yuz207/agentpad13/release/hardware/case/v2/bases/INTERFACE.md

# agentpad13 — tray base interface

**Design your own base.** The tray carries four pockets near its centre. Put
four matching pegs on anything you like and it mounts. The interface does not
care how big your base is or what shape it is.

License: CERN-OHL-W v2. GENERATED by `agentpad13_base.py` — do not hand-edit.

## The datum

The centre of the case outline, in plan. The band outer
(95.6 x 111.4 mm) and the tray outline
(84.3 x 100.1 mm) are **both** centred on it, so you can find
it with a ruler on a finished case. Everything below is measured from there.

**Orientation.** The USB port is on the FAR edge, away from you. The pattern is
4-fold symmetric, so a base fits in any of four 90 deg rotations.

## The four pockets

| | |
|---|---|
| count | 4 |
| diameter | **Ø6.0 mm** |
| depth | **1.6 mm** below the mating plane |
| positions from datum | (-12.5, -12.5), (+12.5, -12.5), (-12.5, +12.5), (+12.5, +12.5) mm |
| square pitch | 25.0 mm (bolt circle Ø35.355) |
| mouth chamfer | 0.2 x 45 deg |
| mating plane | the flat tray bottom — keep all your material below it |

Smallest base that carries the whole pattern with a 3 mm wall:
**Ø47.4 mm.**

## Your pegs

| | |
|---|---|
| length | 1.4 mm — leaves a 0.2 mm gap so the base seats on its FACE, not on peg tips |
| tip chamfer | 0.4 mm |
| fit ladder | **5.6 / 5.7 / 5.8 / 5.9 mm** |
| start with | 5.8 in rigid filament, **5.9 in TPU** |

The tray side is CAD-nominal and carries **no** allowance — all the fit lives on
your peg. Print `stl/base_fit_gauge.stl`, push each peg into any pocket, keep
the rung that holds. The gauge is marked with raised dots: n dots = rung n,
smallest first.

TPU compresses instead of shearing the pocket wall, so it wants the **tight**
rung, not the loose one.

## Load path — read this before you make it thin

Vertical load goes through the **flat mating plane**, never through the pegs.
The pegs locate the base and take shear. Each has
8.4 mm2 of bearing, about 250 N at 30 MPa,
against single-digit-newton service loads. Engagement depth is not your limiting
factor; flatness of the mating face is.

## Keep-outs

- **BOOT / RESET service slots**, x 59.0..76.0, y 83.3..93.3 mm. If
  your base covers this area it **must** carry a through window. A base that
  stays inside **Ø78.36 mm**
  about the datum never reaches it.
- **Feet are not part of the design.** Every base underside is FLAT — no
  recesses, no bolt circle, no prescribed part. Stick on whatever you like,
  wherever you like; every stance figure below EXCLUDES feet.
- **USB face** is on the far edge, above the mating plane. A wedge that raises
  the far edge eats plug-to-desk clearance.

## Will it tip over? (small bases only)

The assembled pad is **176 g**, with its centre of mass within 1 mm of
the datum. A base narrower than the footprint makes it cantilever. The worst
load is a firm press on the **encoder knob edge**, 56 mm out — not the
farthest key.

Minimum base mass for a **circular** base, to hold a 1.5x margin at a 3 N press
and not tip at all at 5 N:

| diameter | >=1.5x at 3 N | no tip at 5 N |
|---|---|---|
| Ø50 | 401 g | 464 g |
| Ø60 | 228 g | 273 g |
| Ø65 | 162 g | 199 g |
| Ø70 | 105 g | 136 g |
| Ø74 | 65 g | 92 g |
| Ø78.0 | 29 g | 52 g |
| Ø80 | 13 g | 33 g |

**This is why the pedestal must be printed SOLID.** At Ø78 its own
printed mass is the only thing resisting the tip, so infill is a structural
setting here, not a speed one. A solid print clears the 5 N abuse case; a normal
3-wall / 20 % gyroid print clears the 3 N design case but not abuse. The
full-footprint `riser` and `wedge` need nothing at all — every control already
sits inside their support polygon.

Full method and the per-part mass model are in
`params/agentpad13_base_params.json` under `stability`. Several inputs are
estimates and are labelled as such — notably the encoder push force, which is
what sizes everything here.

## Reference bases in this folder

| variant | outline | mass | ballast |
|---|---|---|---|
| `riser` | 91.6 x 107.4 full footprint x 3 mm flat | 33 g | none |
| `wedge` | 91.6 x 107.4 full footprint, 8 deg back-raised | 50 g | none |
| `pedestal` | Ø78 tilted drum, 8 deg | 59 g | **print SOLID** — its own mass is the ballast |

All three print **desk face on the bed, no support**.
