yuz207/agentpad13/firmware/CODEX-OAI-SOURCE.md

# AgentPad13 direct-OAI source snapshot

This directory is the buildable source hand-off for the AgentPad13 Direct OAI
firmware. The original snapshot came from the `agentpad13-direct-oai` worktree
on branch `dev`, based at commit
`567efcba52709e7850540b5100361c0d85734b8e`, including the working-tree fixes
present when that snapshot was assembled. The destination port has since been
rebuilt from the reviewed AgentPad13 source; the current artifact facts below
supersede the snapshot candidate.
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
