yuz207/agentpad13/release/hardware/case/v2/bases/renders/bases.png

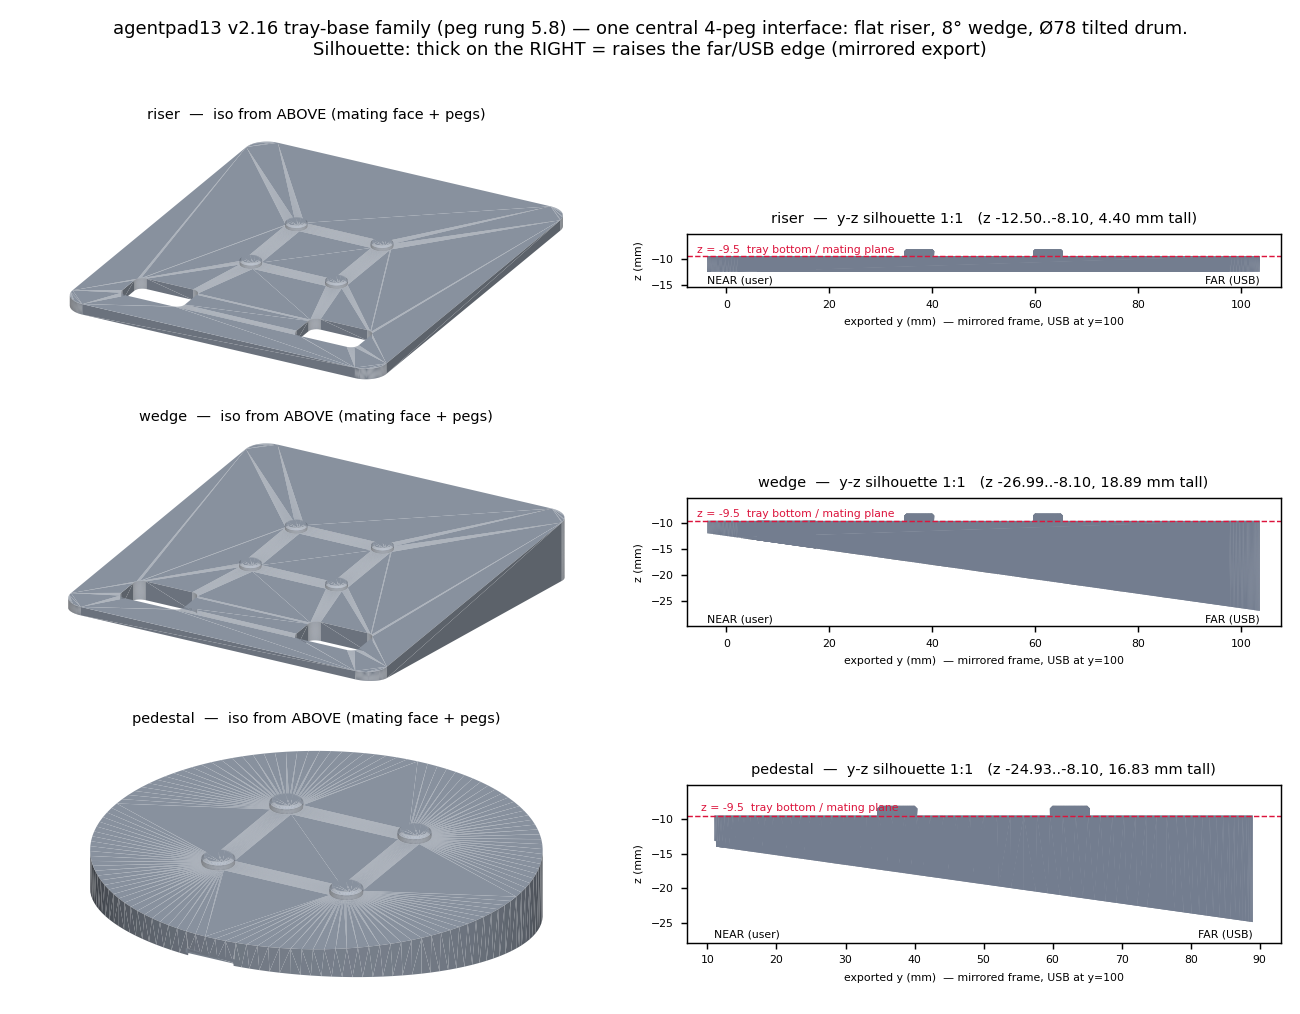
release/hardware/case/v2/bases/renders/bases.png
