yuz207/agentpad13/release/hardware/case/v2/fab/agentpad13_v2_plate_v5_top.png

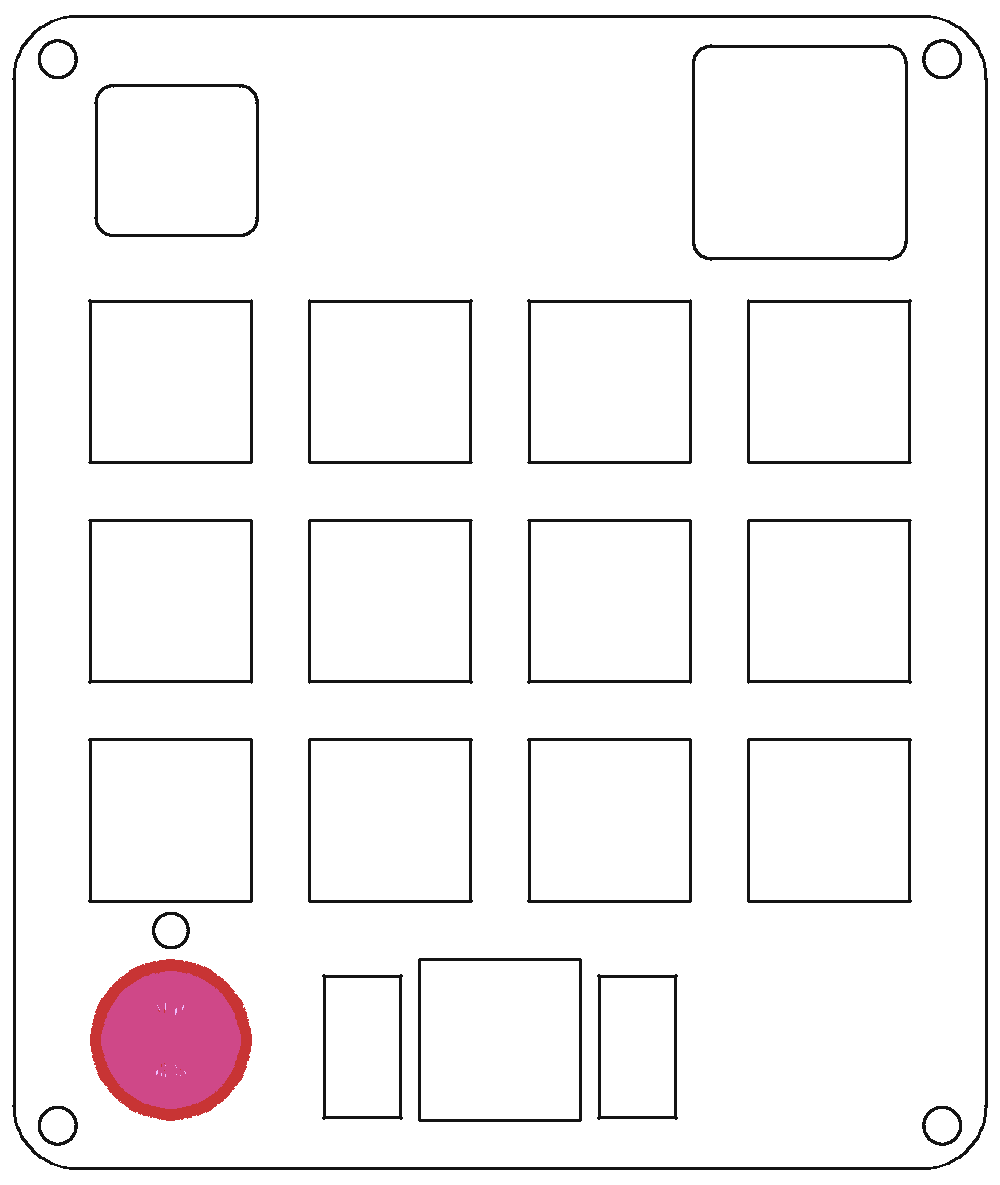
release/hardware/case/v2/fab/agentpad13_v2_plate_v5_top.png
