yuz207/agentpad13/release/hardware/case/v2/gasket/gasket_template.png

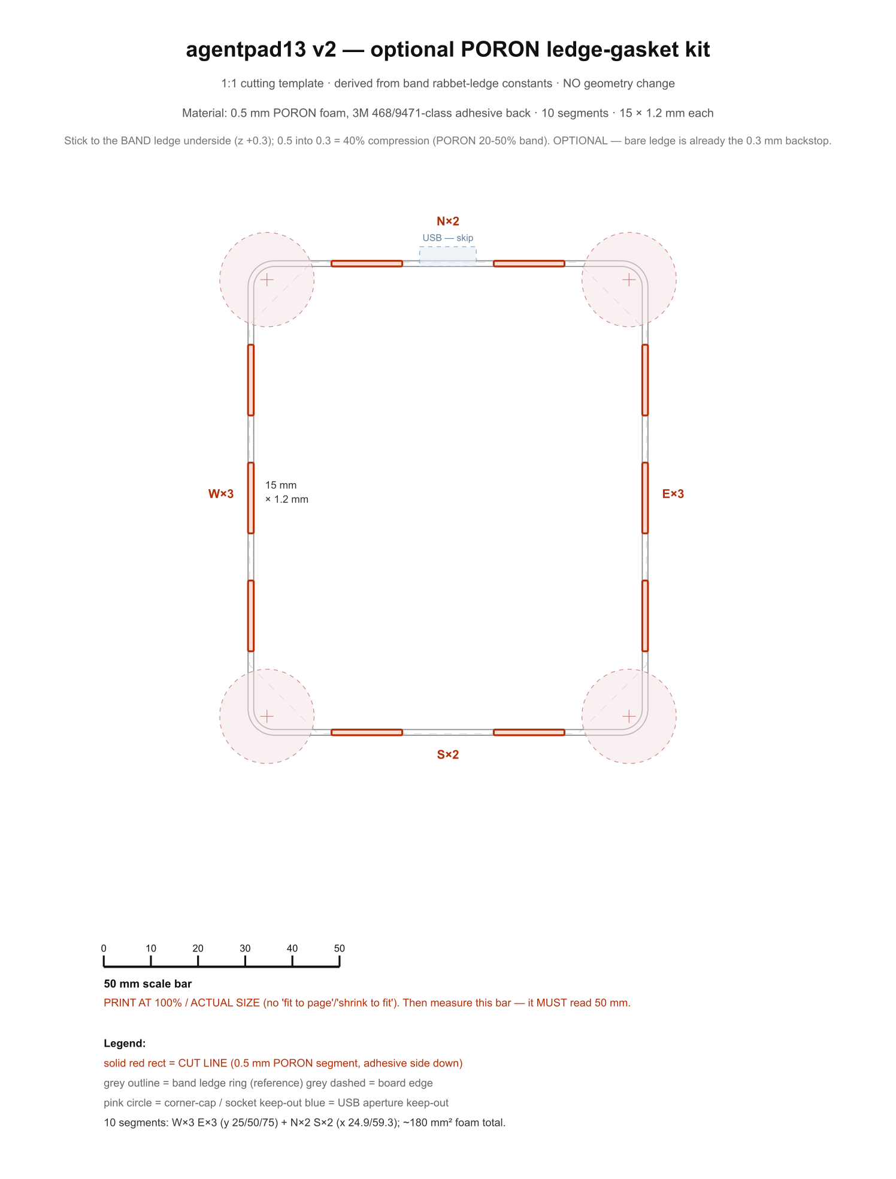
release/hardware/case/v2/gasket/gasket_template.png
