yuz207/agentpad13/release/hardware/pcb/v5_8_orient.png

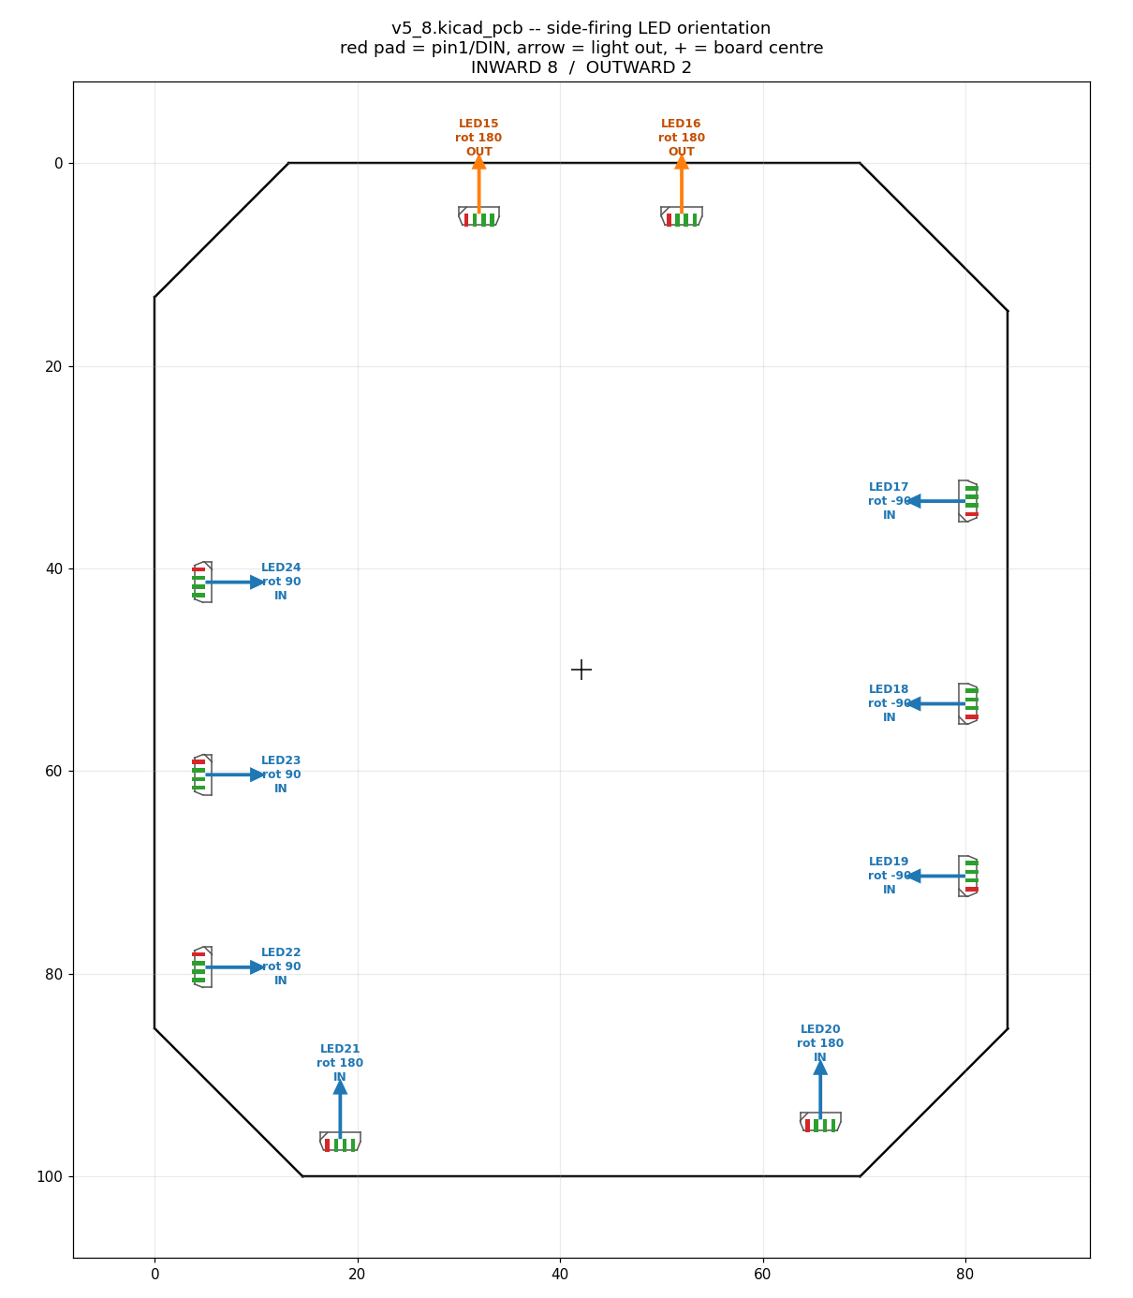
release/hardware/pcb/v5_8_orient.png
