yuz207/agentpad13/release/hardware/pcb/v5_8_render_top.png

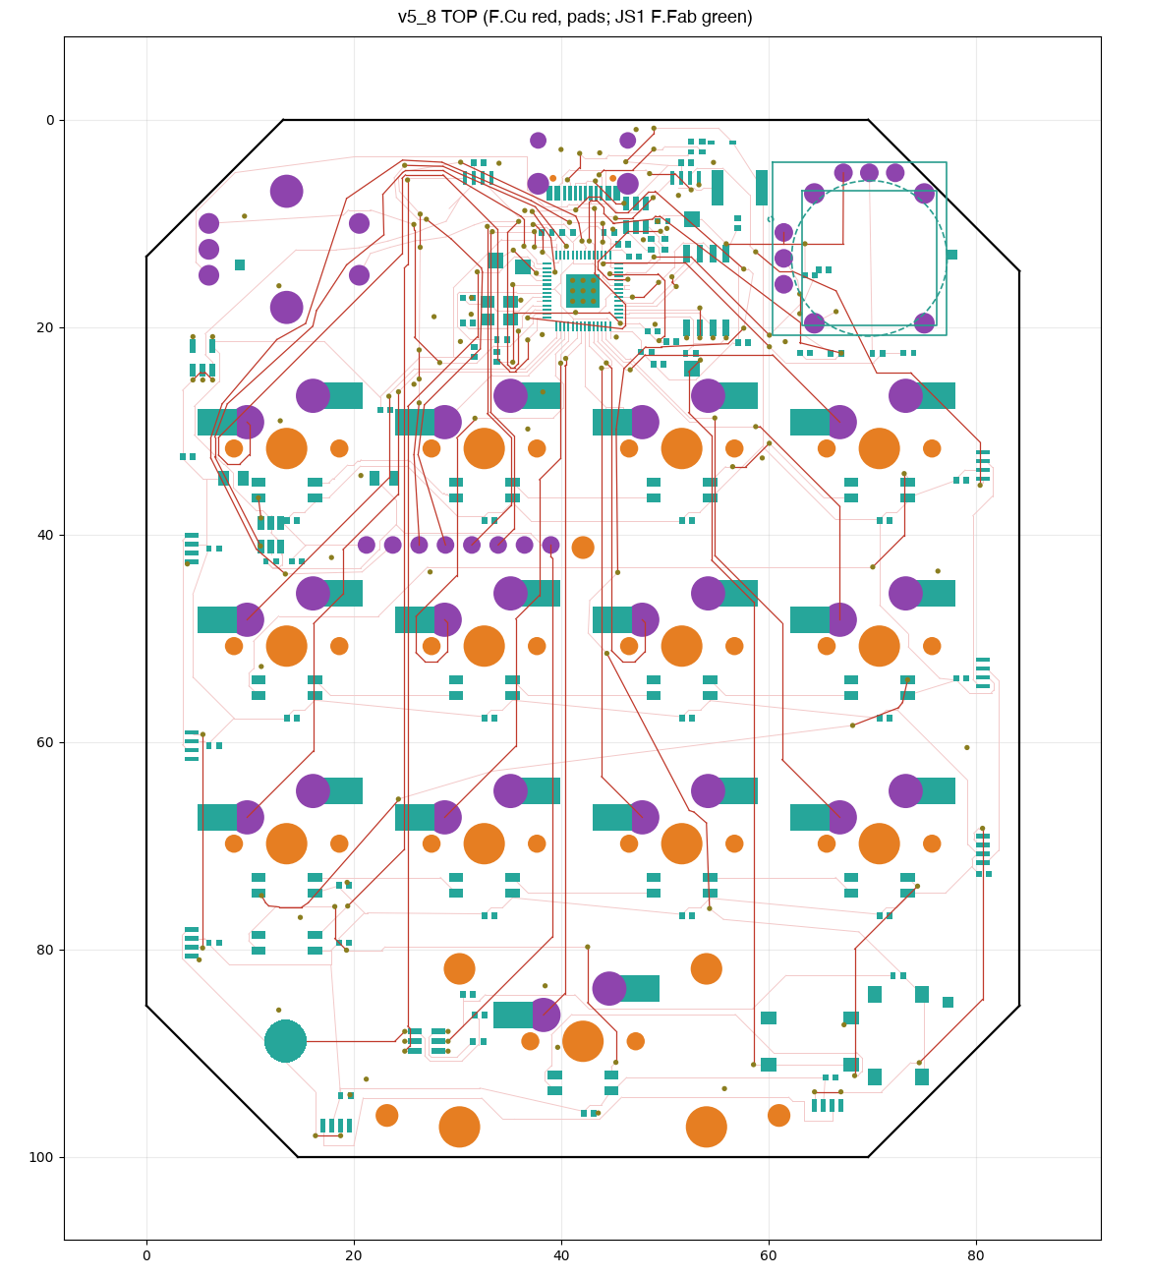
release/hardware/pcb/v5_8_render_top.png
