yuz207/agentpad13/release/renders/js1_pad_swap.png

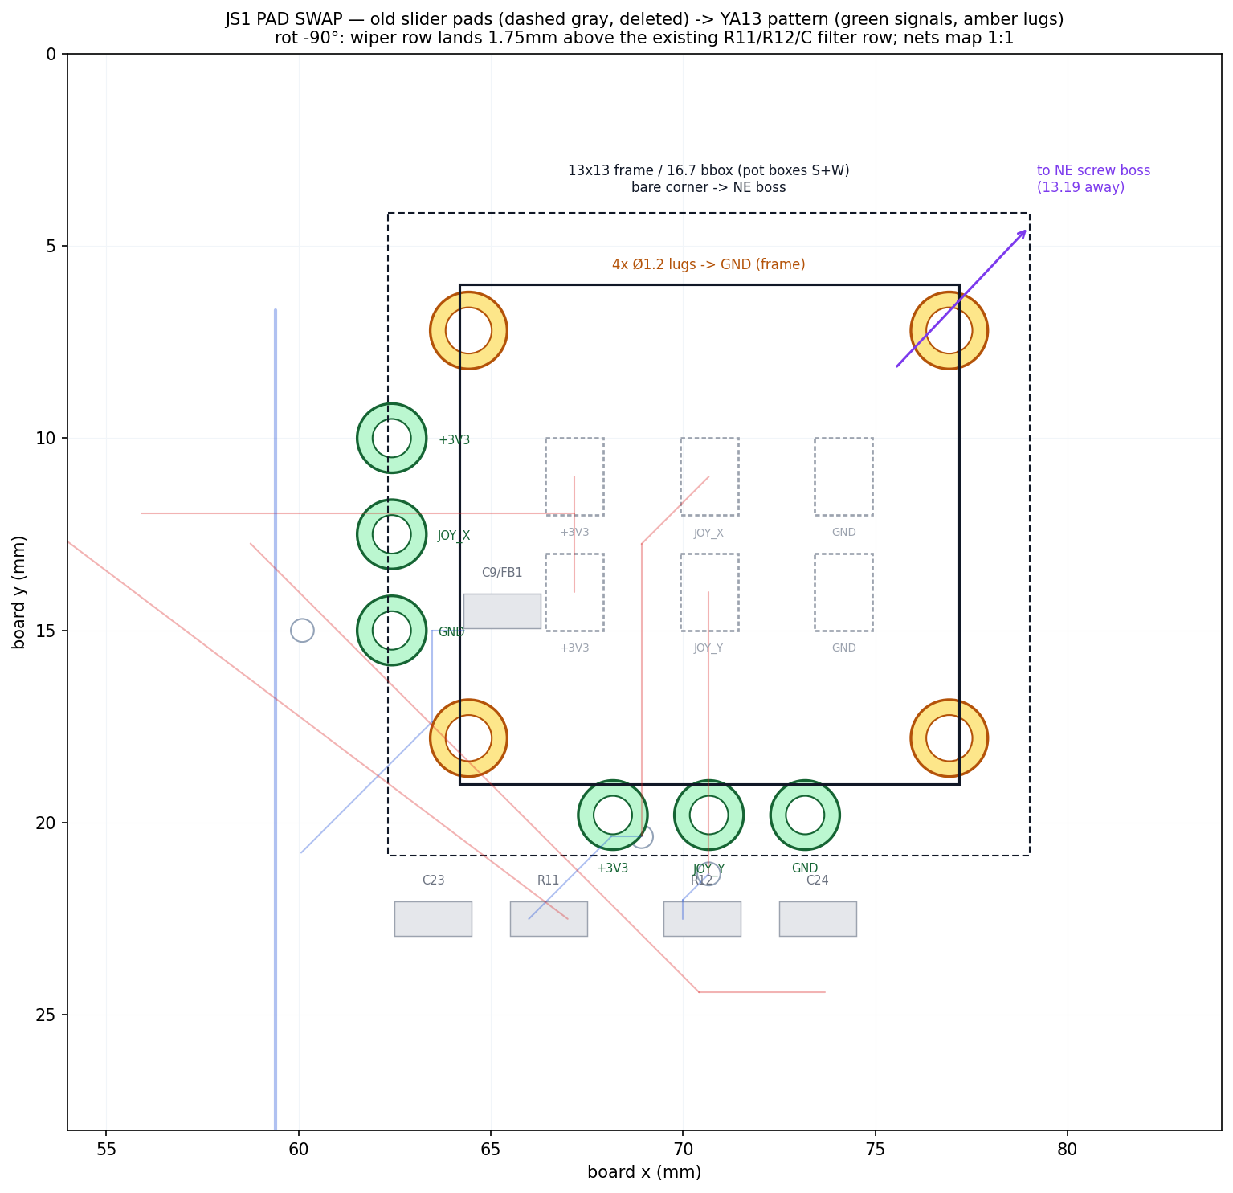
release/renders/js1_pad_swap.png
