yuz207/agentpad13/release/renders/v24_corner_notch.png

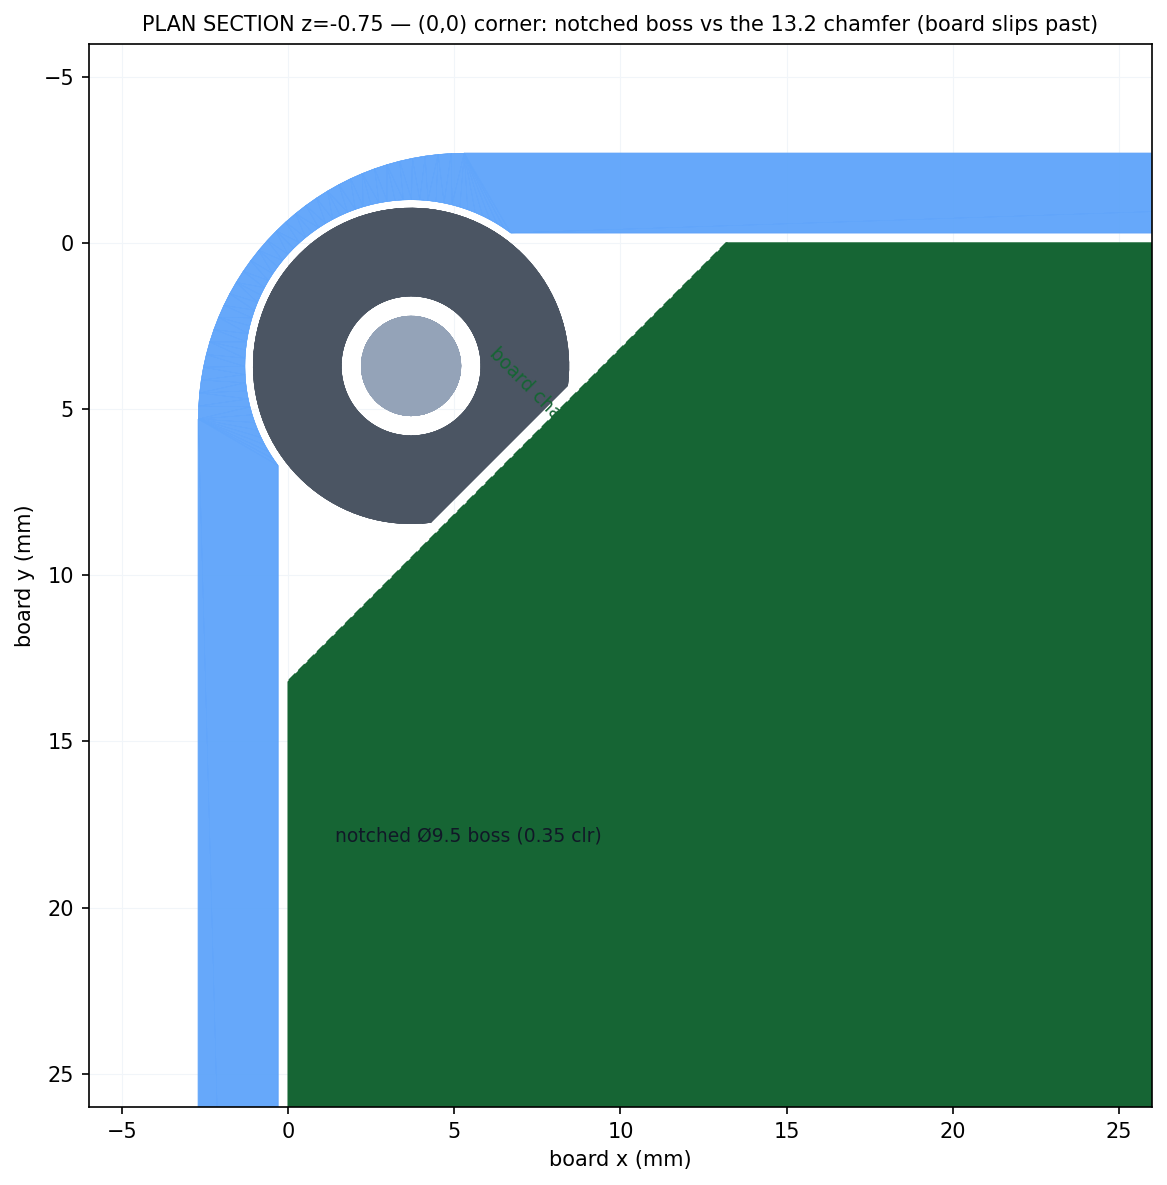
release/renders/v24_corner_notch.png
