yuz207/agentpad13/release/renders/v24_js_zone.png

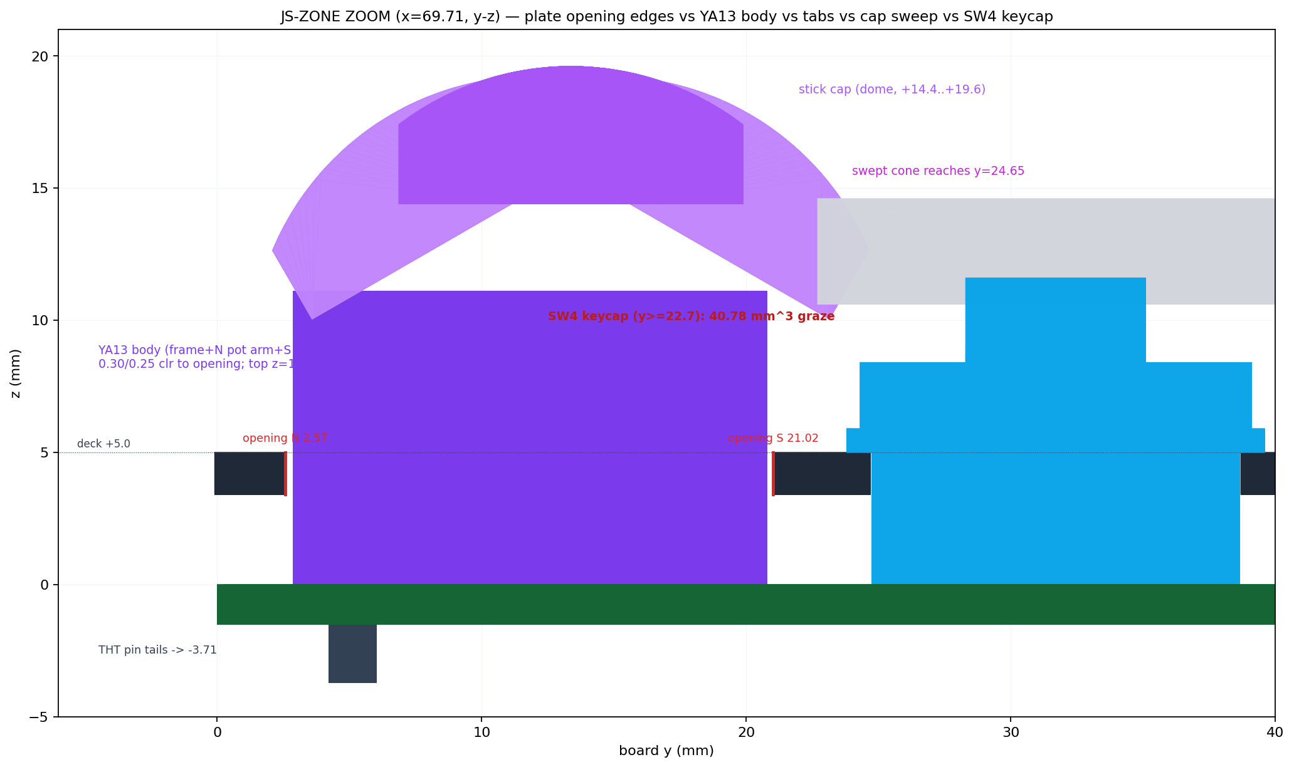
release/renders/v24_js_zone.png
