yuz207/agentpad13/release/renders/v24_js_zone_chamfer_STOP.png

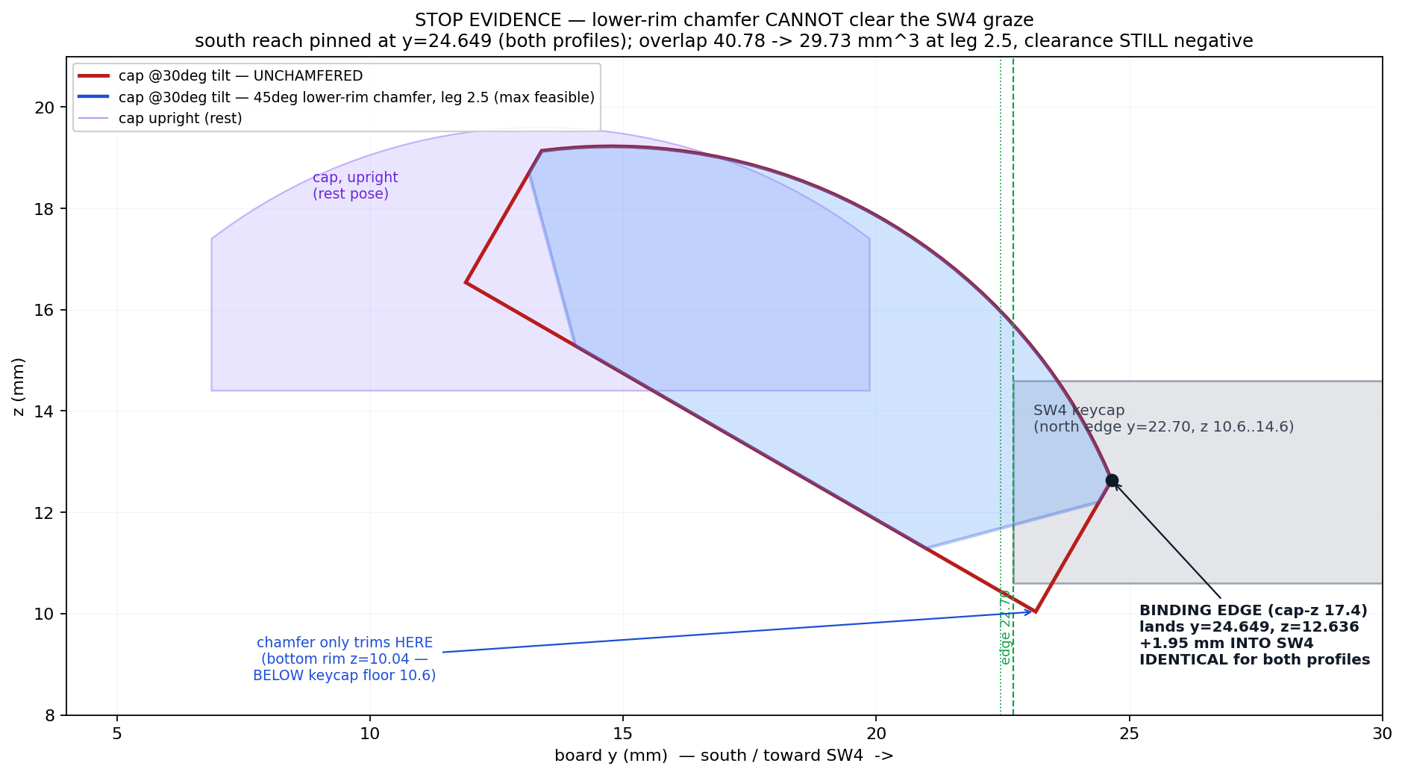
release/renders/v24_js_zone_chamfer_STOP.png
