yuz207/agentpad13/release/renders/v24_section_controls.png

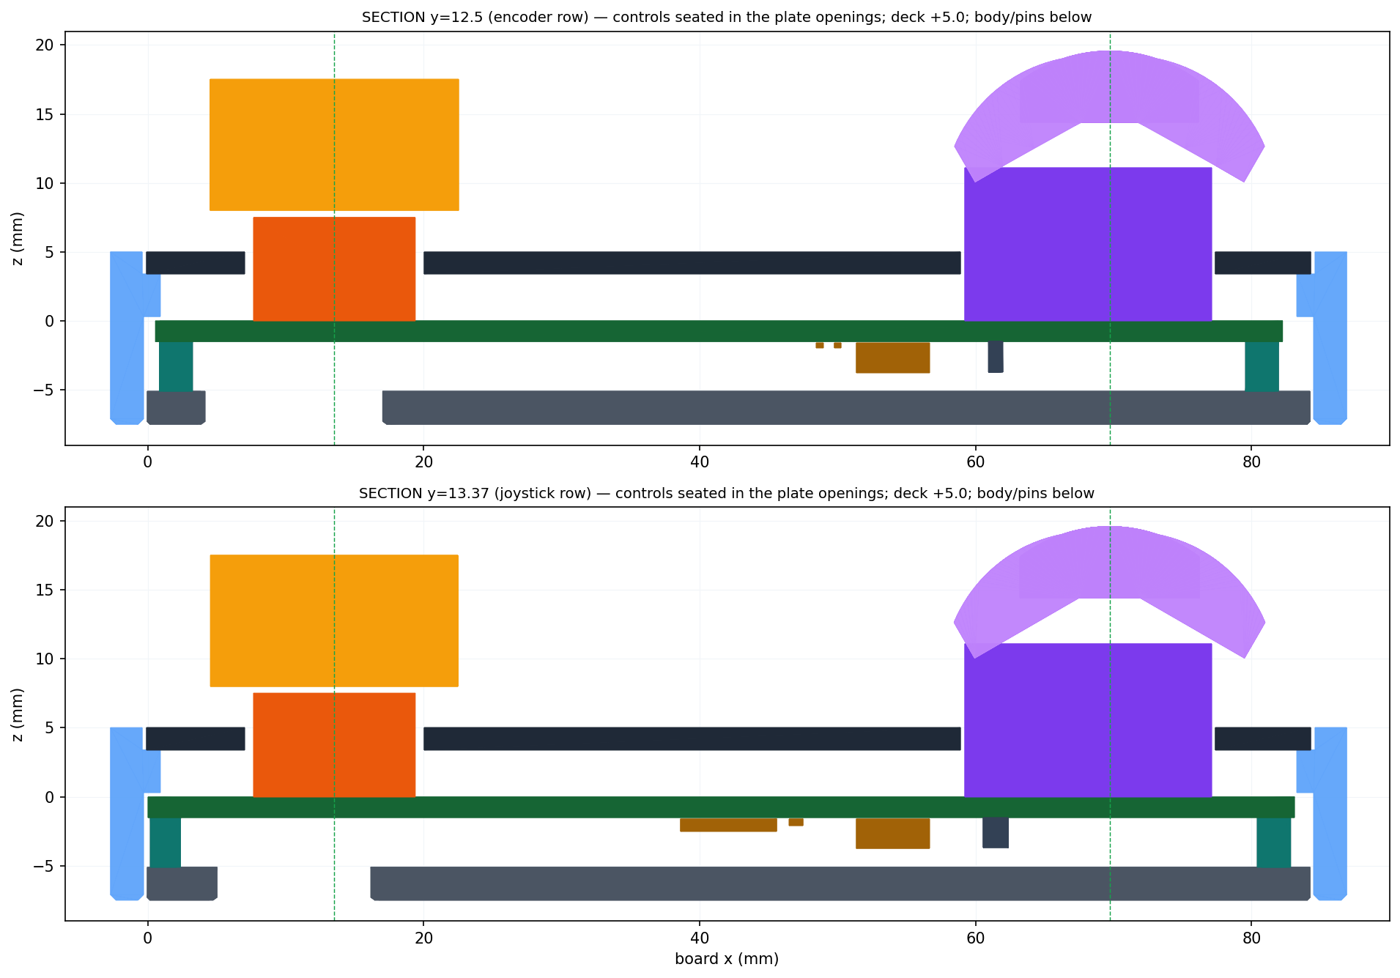
release/renders/v24_section_controls.png
