yuz207/agentpad13/release/renders/v24_section_stickcol.png

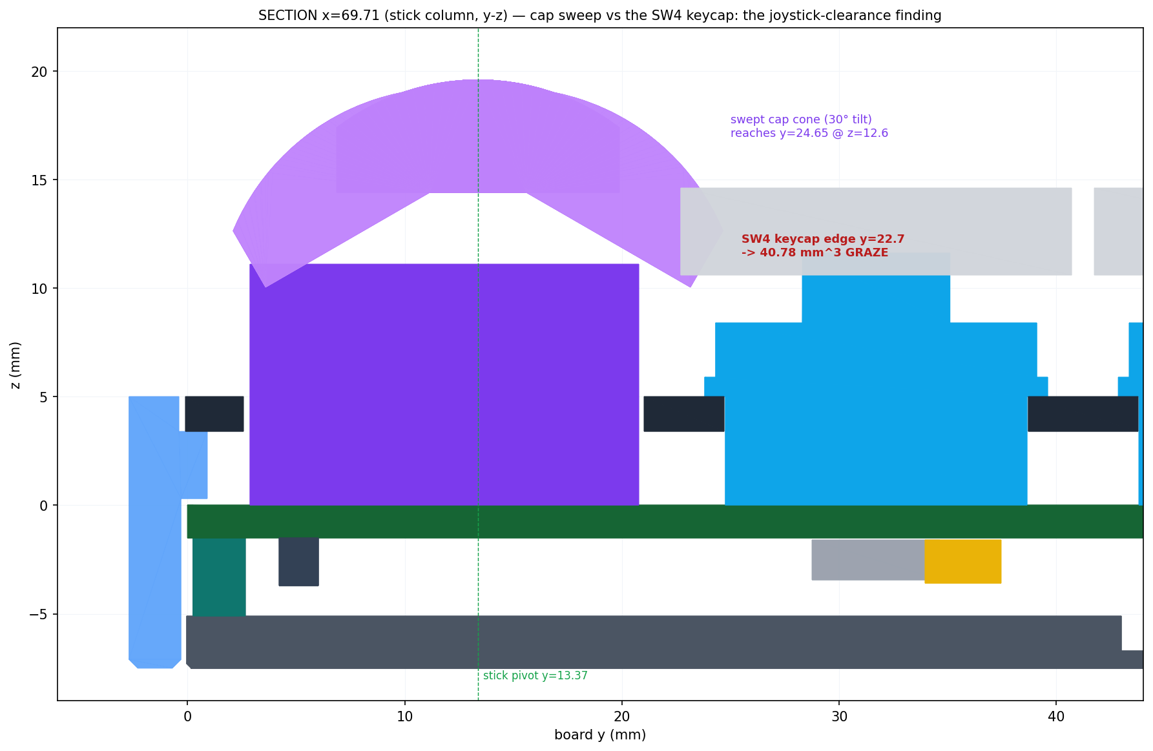
release/renders/v24_section_stickcol.png
