yuz207/agentpad13/release/renders/v24_section_usb.png

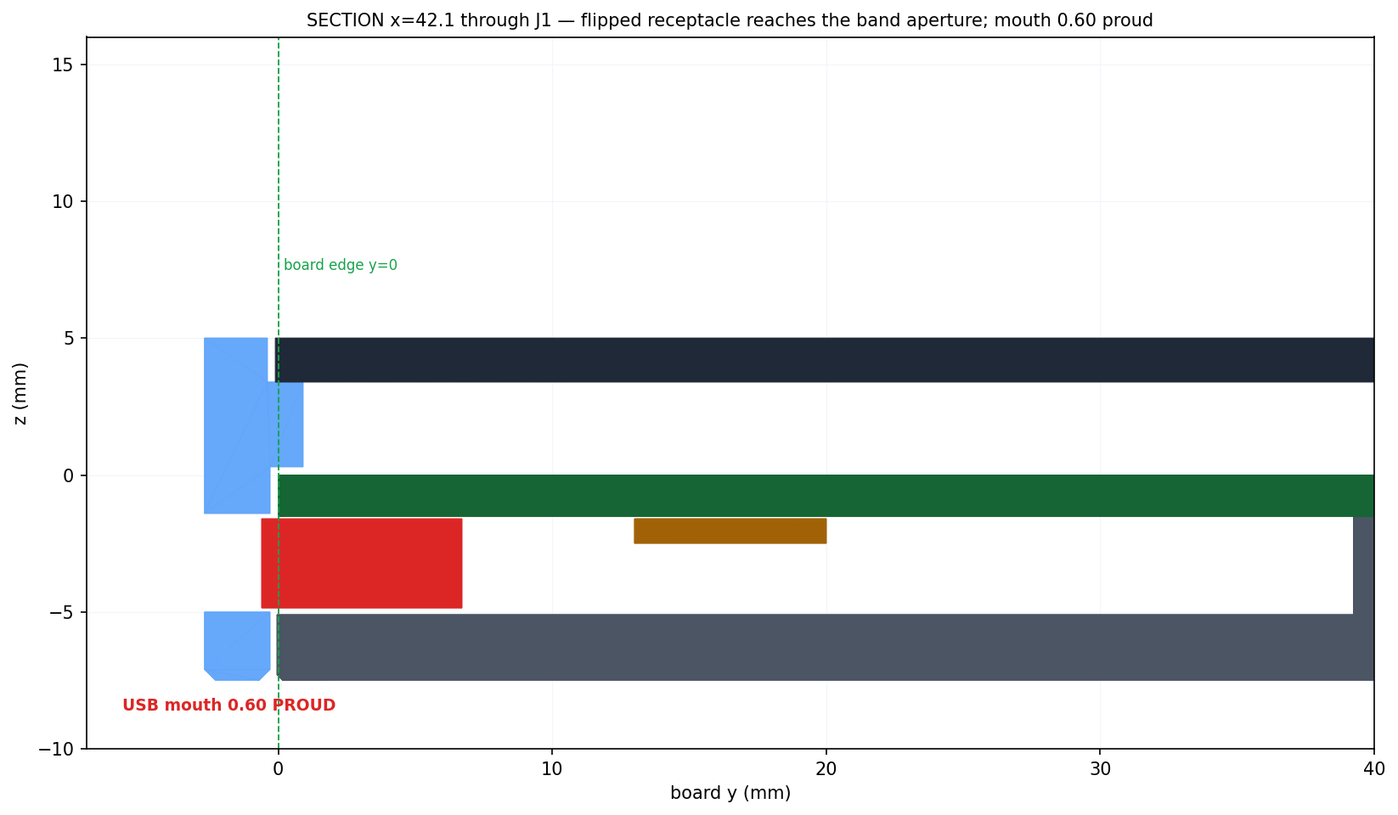
release/renders/v24_section_usb.png
