yuz207/agentpad13/release/renders/v24_side_elevations.png

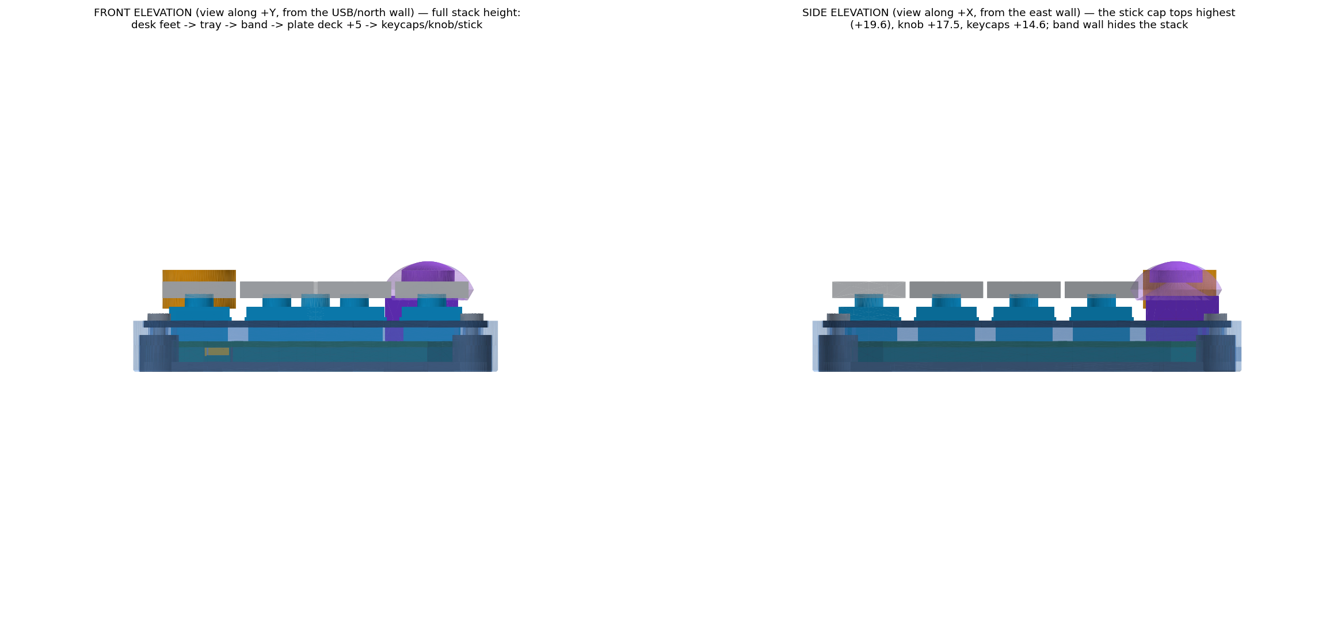
release/renders/v24_side_elevations.png
