yuz207/agentpad13/release/renders/v25_cap_taper_vs_dome.png

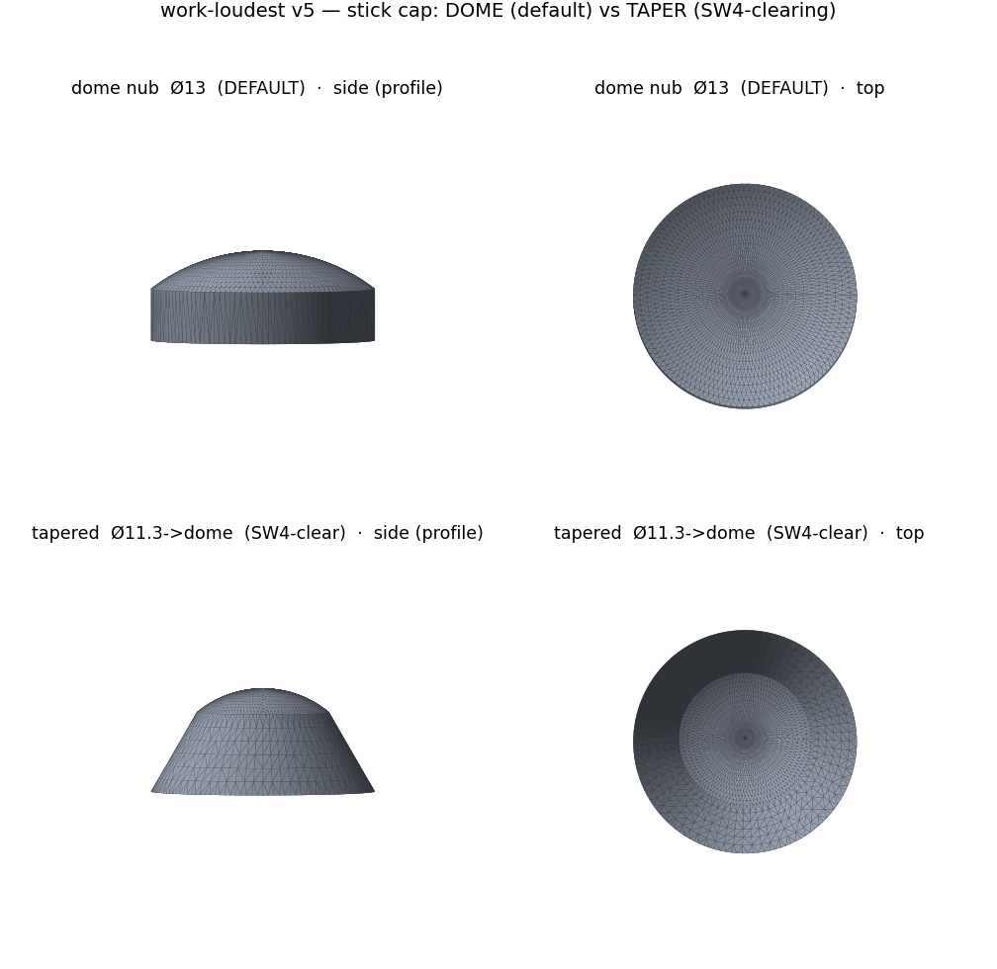
release/renders/v25_cap_taper_vs_dome.png
