yuz207/agentpad13/release/renders/v25_height_ladder.png

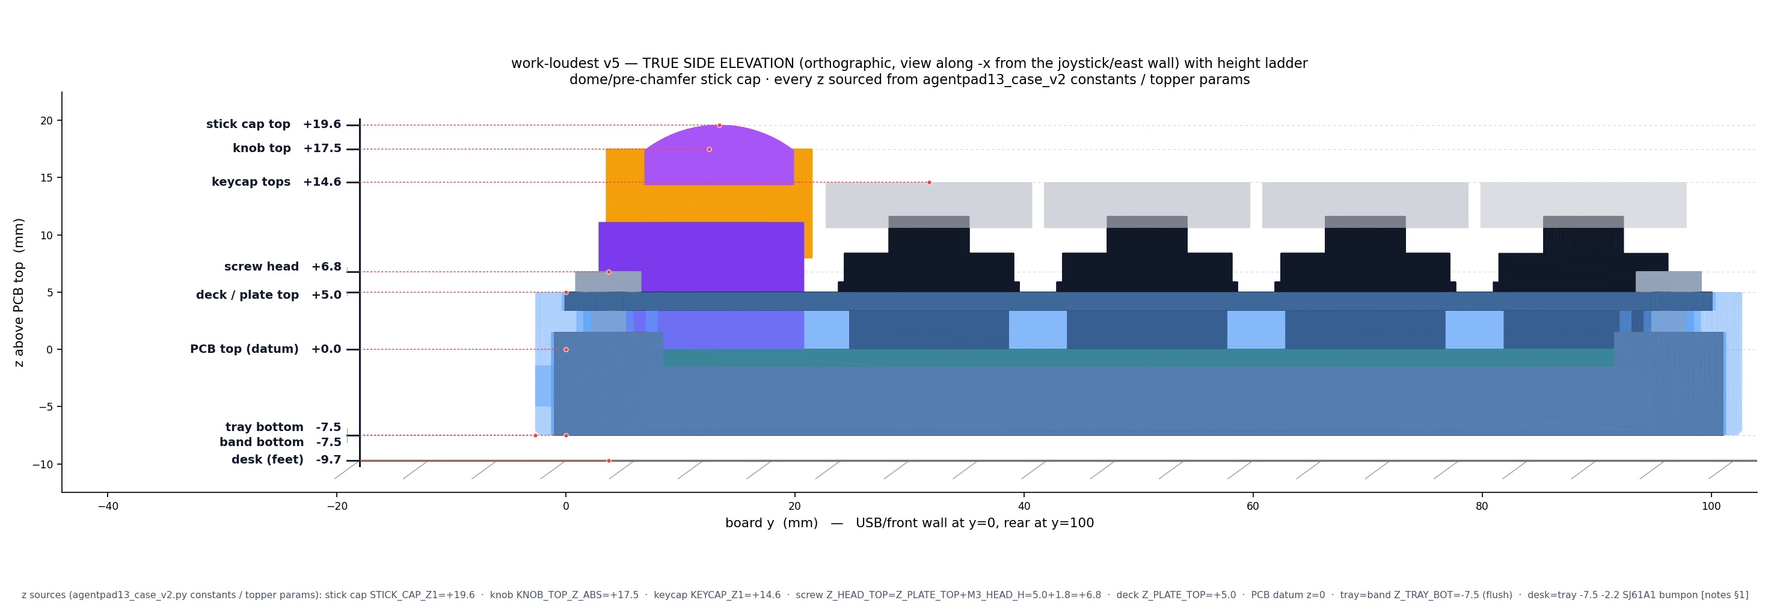
release/renders/v25_height_ladder.png
