yuz207/agentpad13/release/renders/v27_turntable.png

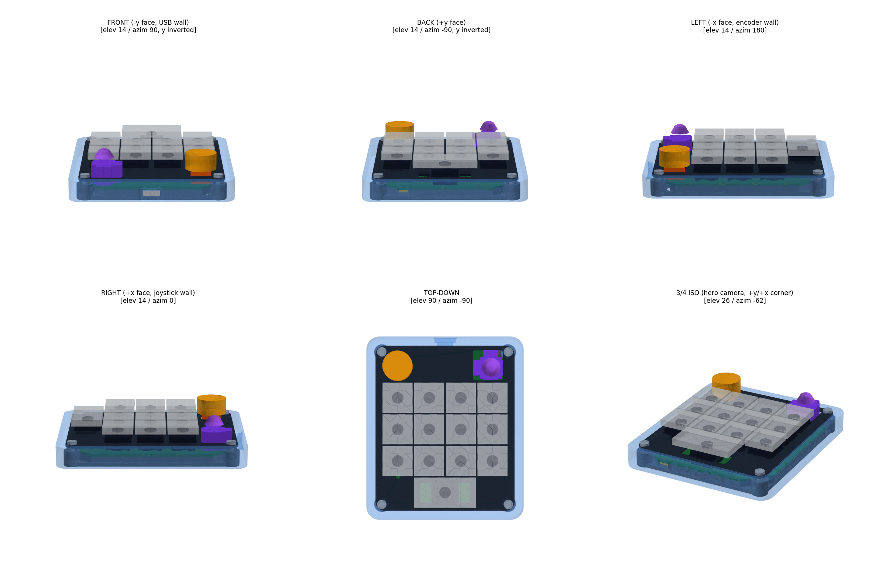
release/renders/v27_turntable.png
