yuz207/agentpad13/release/hardware/case/v2/step/agentpad13_v2_plate.step

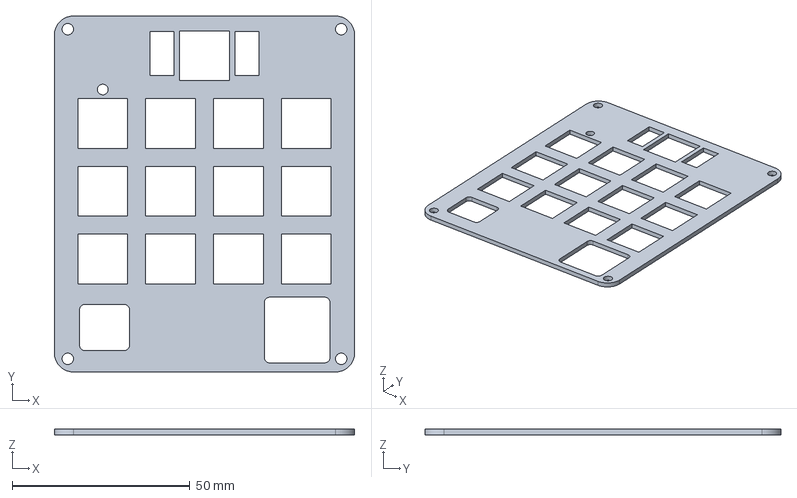
[picture p38: CAD file, 2026-08-20]
release/hardware/case/v2/step/agentpad13_v2_plate.step
84.4 x 100.0 x 1.60 mm
