yuz207/agentpad13/release/hardware/case/v2/toppers/stl/stick_puck_v2_TPU_cell2.stl

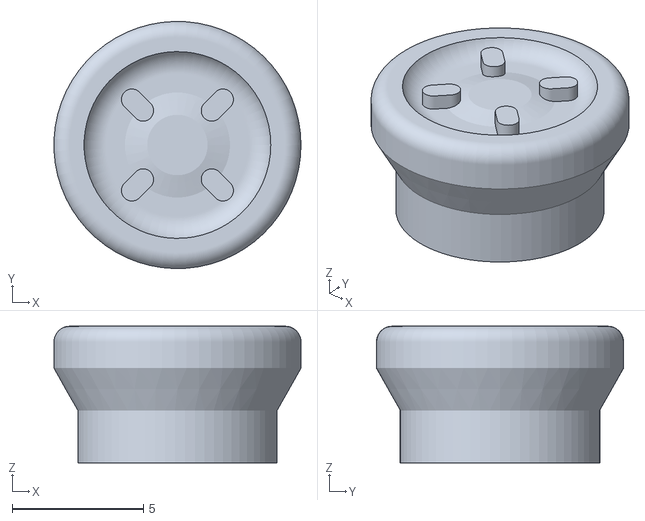
[picture p39: CAD file, 2026-08-24]
release/hardware/case/v2/toppers/stl/stick_puck_v2_TPU_cell2.stl
9.41 x 9.41 x 5.20
