yuz207/agentpad13/release/hardware/PCBWay_keycaps_boxfit_2026-07-24/cap_dish_1u_17p5_boxfit.stl

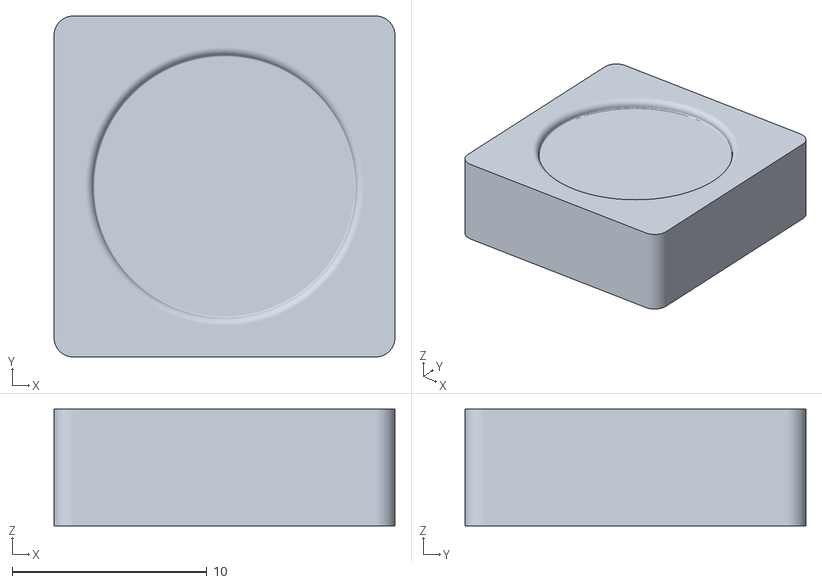
[picture p40: CAD file, 2026-07-25]
release/hardware/PCBWay_keycaps_boxfit_2026-07-24/cap_dish_1u_17p5_boxfit.stl
17.5 x 17.5 x 6.00
