yuz207/agentpad13/release/hardware/case/v2/step/agentpad13_v2_band_1.6mm_w7.4.step

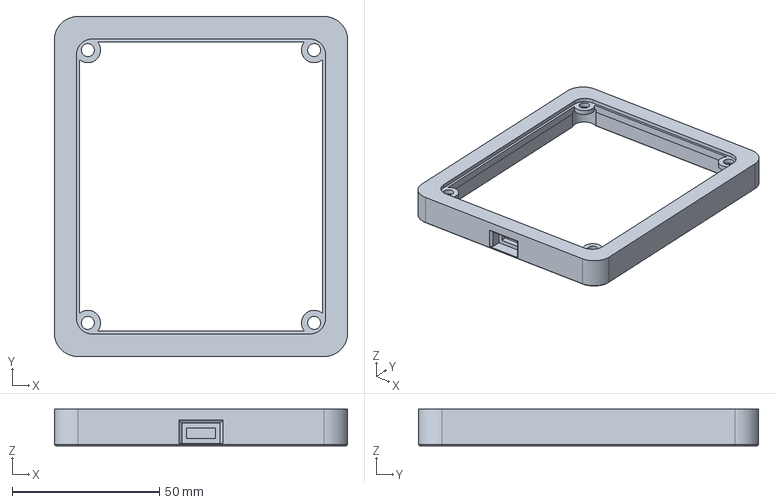
[picture p41: CAD file, 2026-08-20]
release/hardware/case/v2/step/agentpad13_v2_band_1.6mm_w7.4.step
99.6 x 115.4 x 12.5 mm
