yuz207/agentpad13/release/hardware/case/v2/toppers/stl/knob_v2_B2_clearance_low.stl

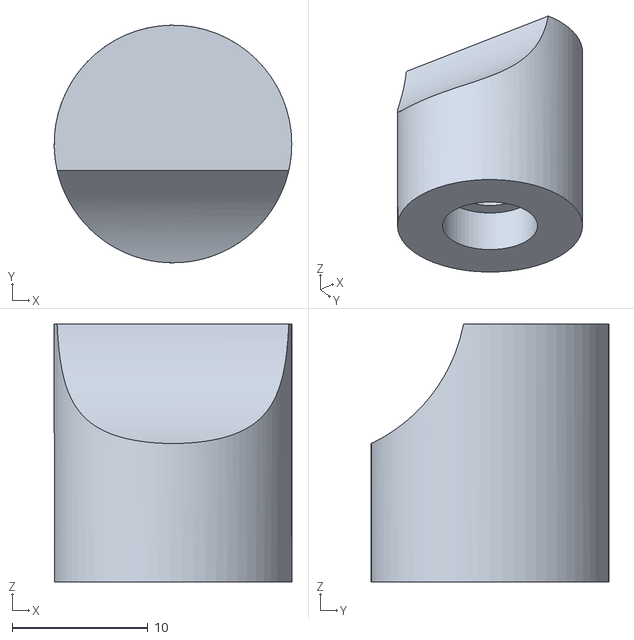
[picture p44: CAD file, 2026-08-23]
release/hardware/case/v2/toppers/stl/knob_v2_B2_clearance_low.stl
17.5 x 17.5 x 19.0
