yuz207/agentpad13/release/hardware/PCBWay_keycaps_boxfit_2026-07-24/cap_dish_2u_stab_17p5_boxfit.stl

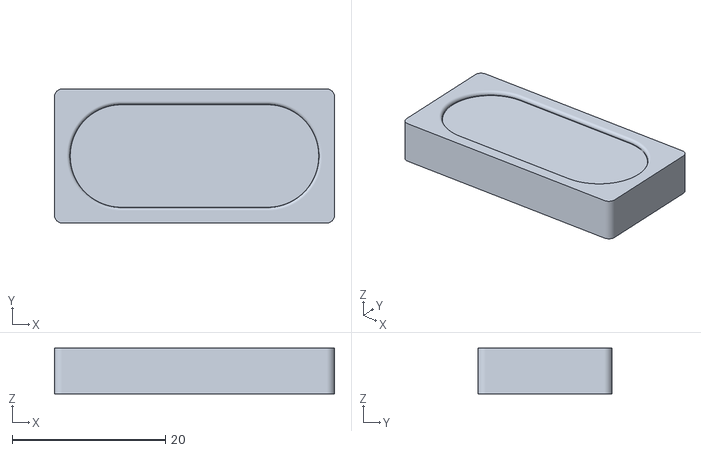
[picture p47: CAD file, 2026-07-25]
release/hardware/PCBWay_keycaps_boxfit_2026-07-24/cap_dish_2u_stab_17p5_boxfit.stl
36.5 x 17.5 x 6.00
