yuz207/agentpad13/release/hardware/PCBWay_keycaps_boxfit_2026-07-24/cap_plateau_2u_boxfit.stl

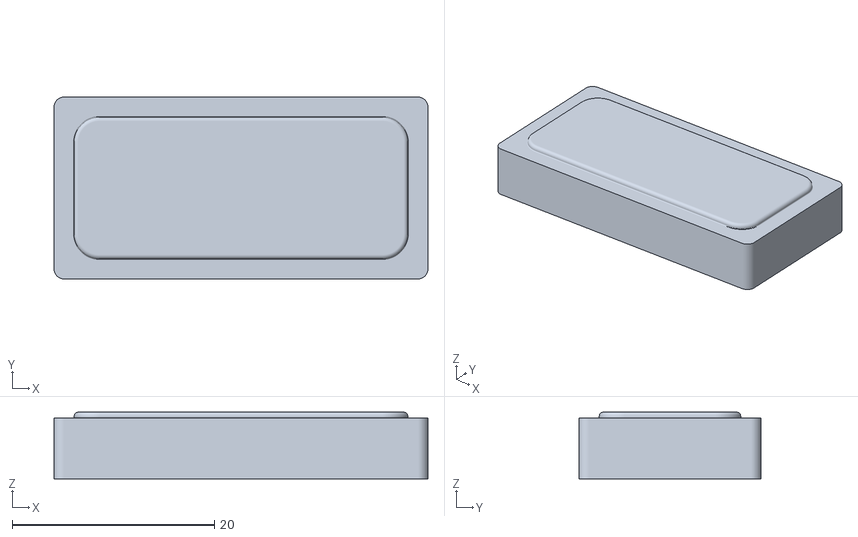
[picture p52: CAD file, 2026-07-25]
release/hardware/PCBWay_keycaps_boxfit_2026-07-24/cap_plateau_2u_boxfit.stl
37.0 x 18.0 x 6.60
