yuz207/agentpad13/release/hardware/case/v2/bases/stl/base_fit_gauge.stl

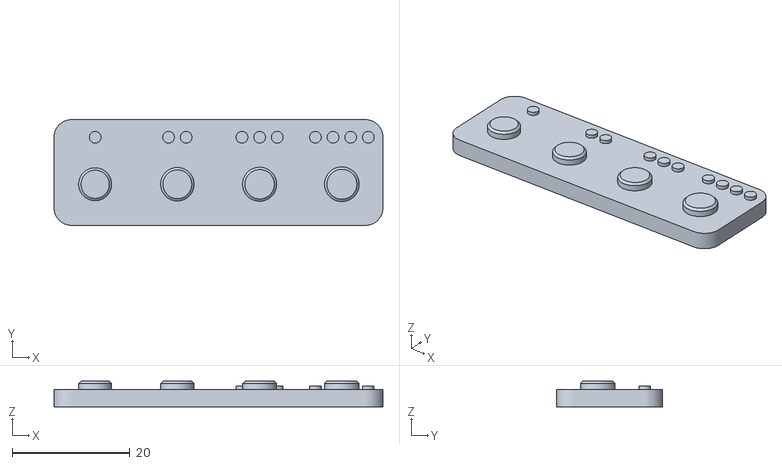
[picture p53: CAD file, 2026-08-20]
release/hardware/case/v2/bases/stl/base_fit_gauge.stl
56.0 x 18.0 x 4.40
