yuz207/agentpad13/configurator/build/out/chirality_check.png

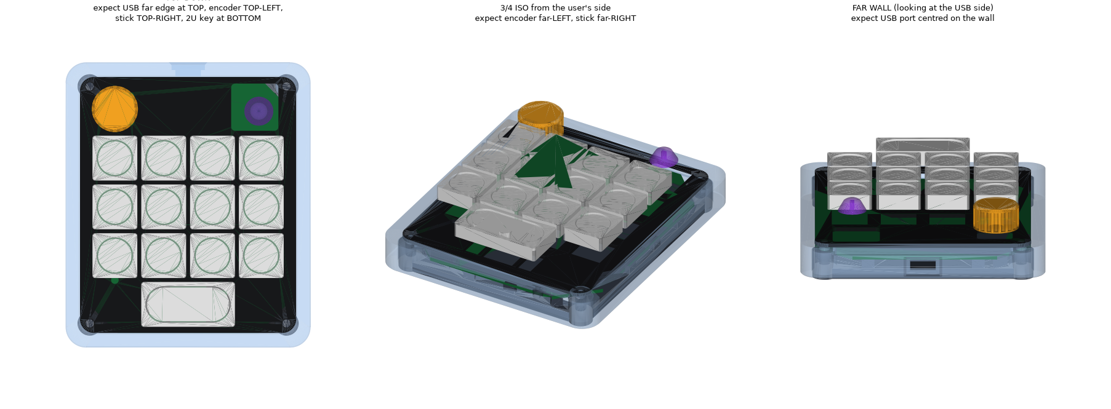
configurator/build/out/chirality_check.png
