yuz207/agentpad13/configurator/build/out/meshes/board_top.png

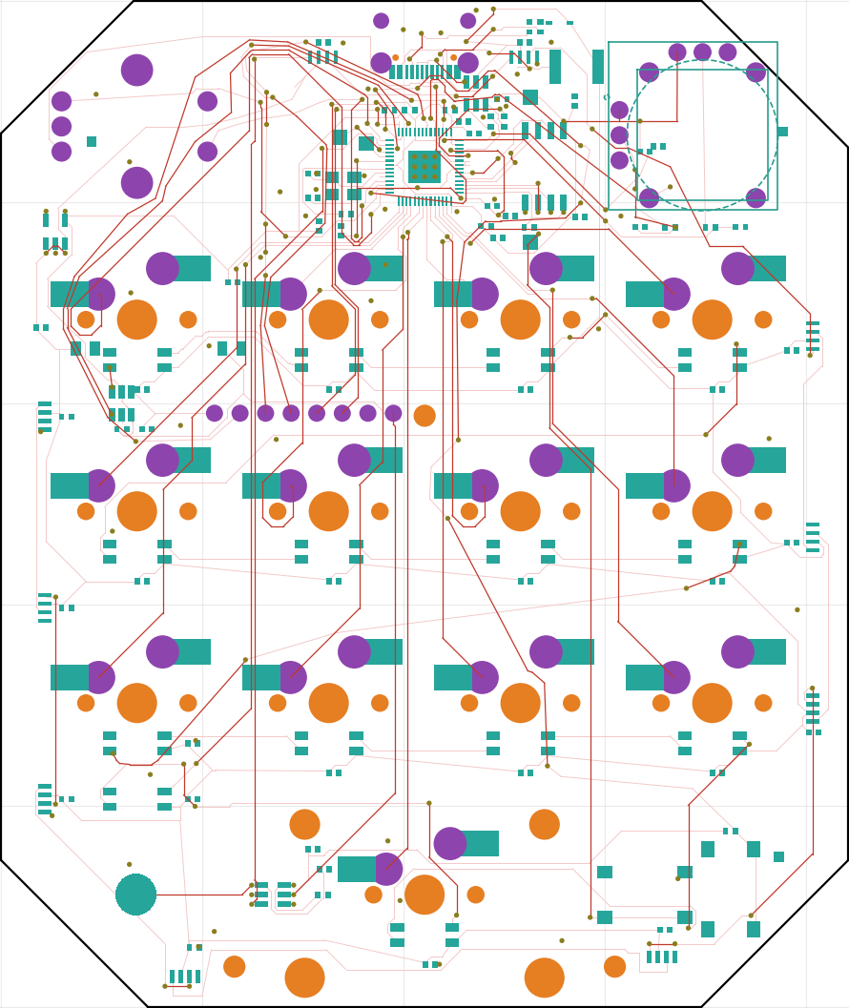
configurator/build/out/meshes/board_top.png
