yuz207/agentpad13/configurator/build/out/textures/plate_decal_standard.png

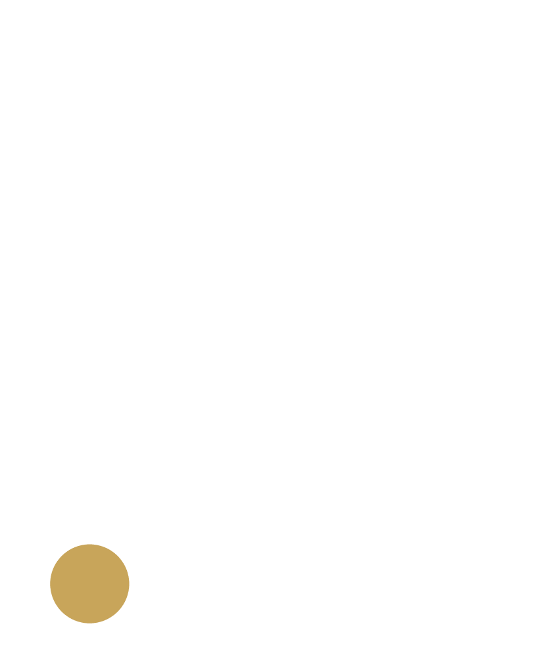
configurator/build/out/textures/plate_decal_standard.png
