yuz207/agentpad13/configurator/build/out/textures/plate_decal_tented_ring.png

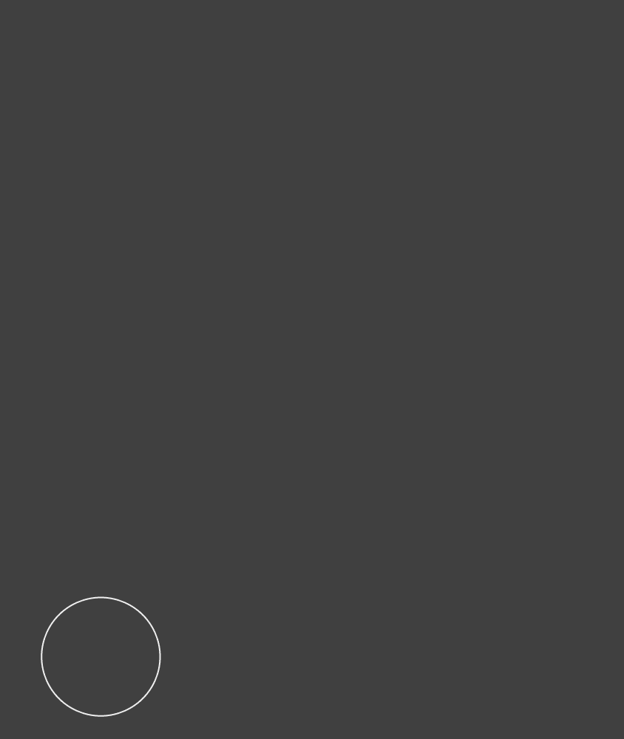
configurator/build/out/textures/plate_decal_tented_ring.png
