yuz207/agentpad13/configurator/build/out/textures/plate_openings.png

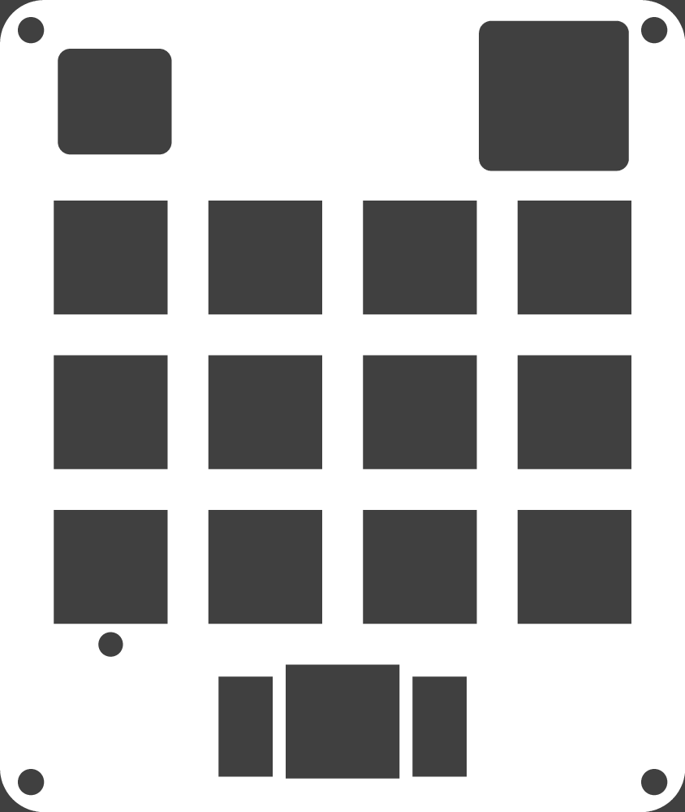
configurator/build/out/textures/plate_openings.png
