yuz207/agentpad13/release/renders/v24_assembled_iso.png

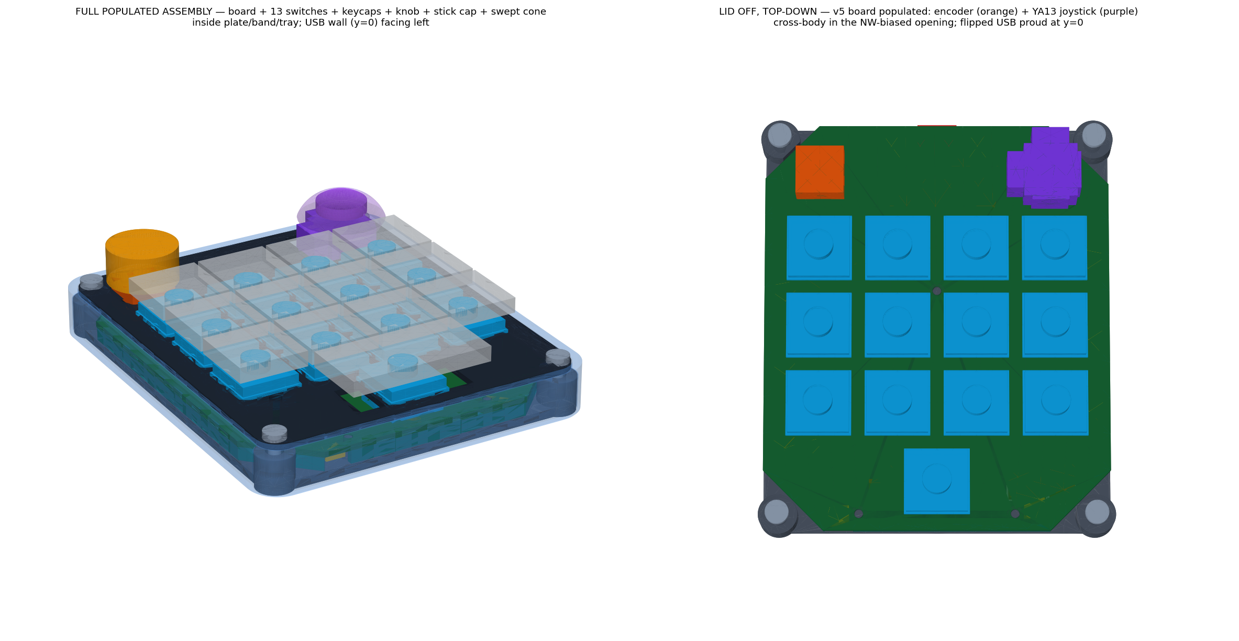
release/renders/v24_assembled_iso.png
