yuz207/agentpad13/release/renders/v27_assembly_front.png

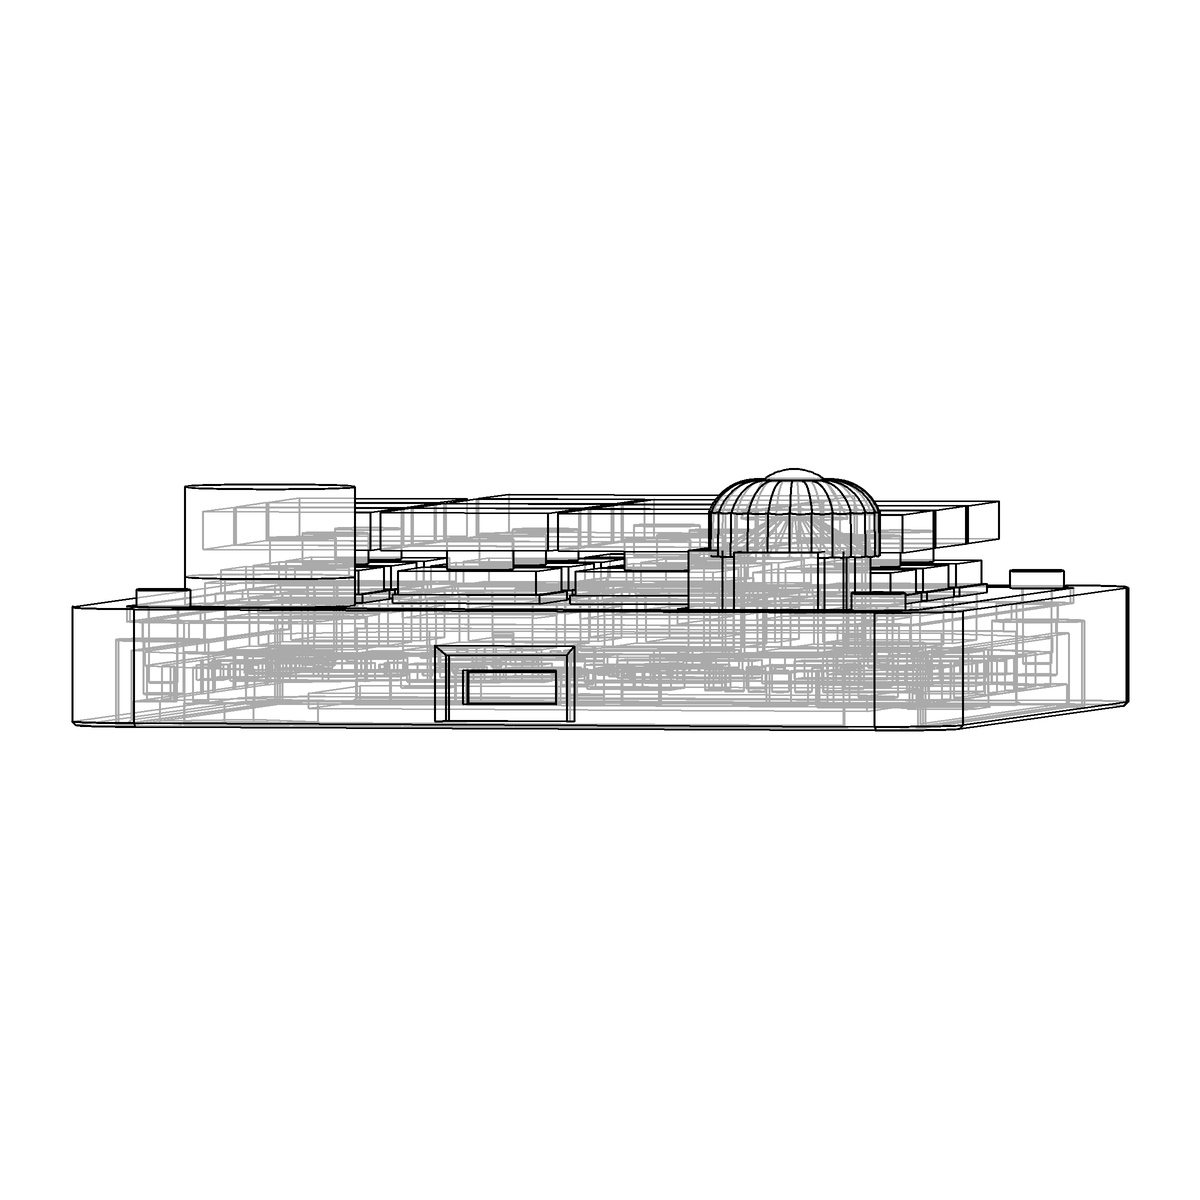
release/renders/v27_assembly_front.png
