yuz207/agentpad13/release/renders/v27_assembly_iso.png

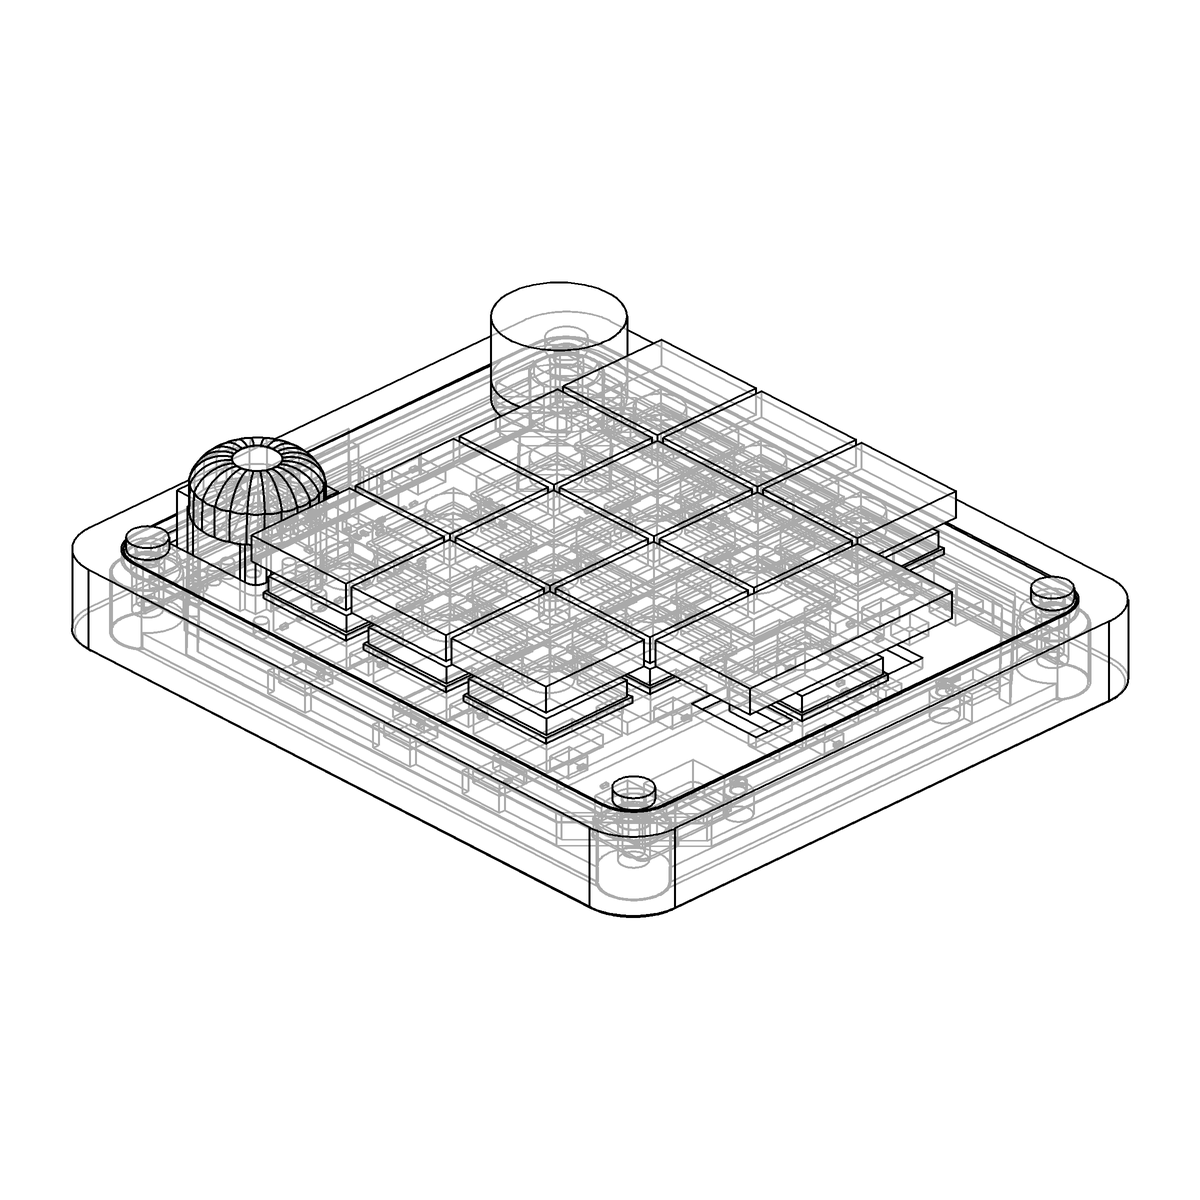
release/renders/v27_assembly_iso.png
